sparkfun/SuperHeadphones/docs/assets/board_files/Super_Headphones_Dimensions.png

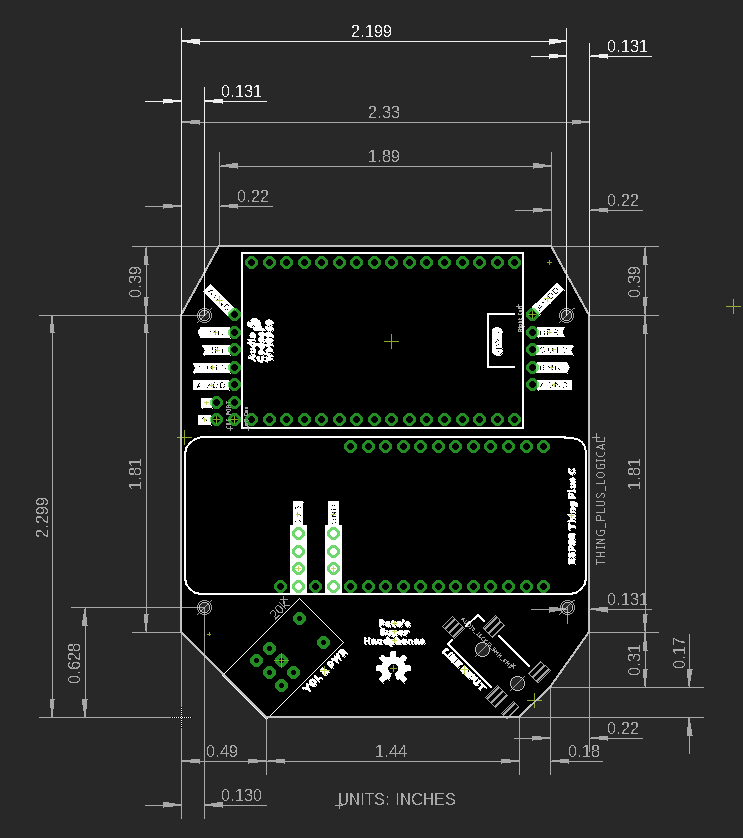
docs/assets/board_files/Super_Headphones_Dimensions.png
