sparkfun/SuperHeadphones/docs/assets/img/cell_bt_connect.jpg

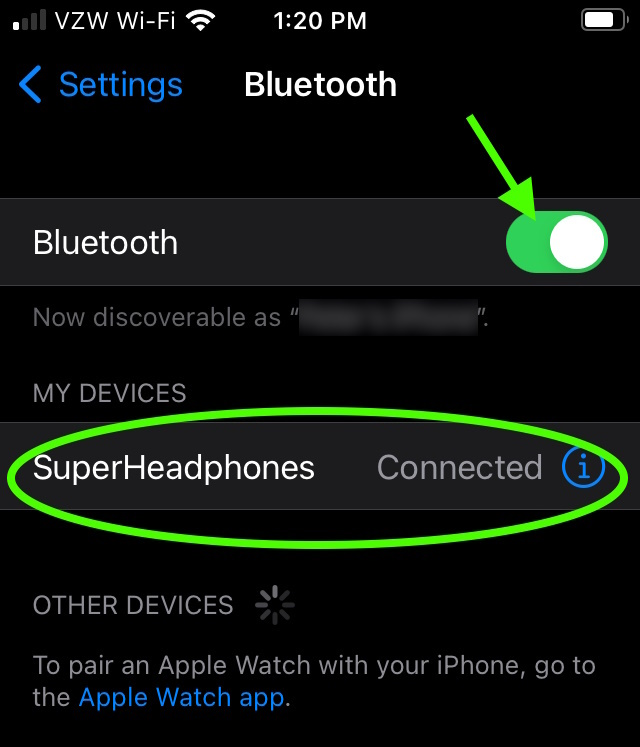
docs/assets/img/cell_bt_connect.jpg
