sparkfun/SuperHeadphones/docs/assets/img/hps_315wide.jpg

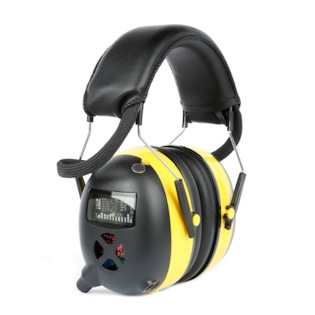
docs/assets/img/hps_315wide.jpg
