sparkfun/SuperHeadphones/docs/assets/img/pc_bt_connect.png

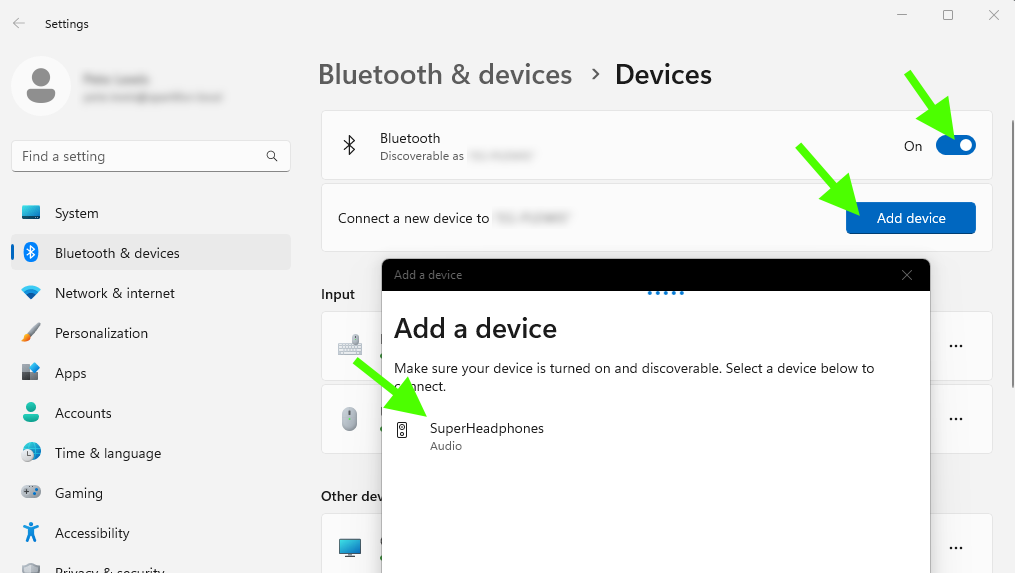
docs/assets/img/pc_bt_connect.png
