sparkfun/SuperHeadphones/docs/assets/img/pete_rotate.gif

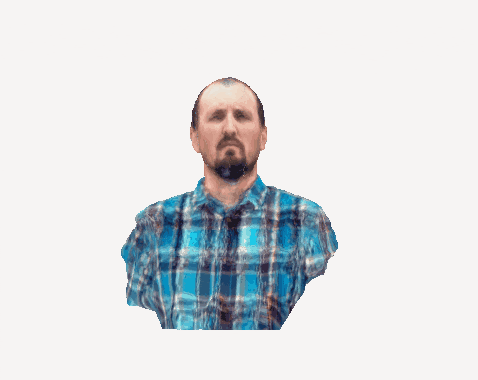
docs/assets/img/pete_rotate.gif
