sparkfun/SuperHeadphones/docs/assets/img/Super_Headphones_Block_Diagram_v01.jpg

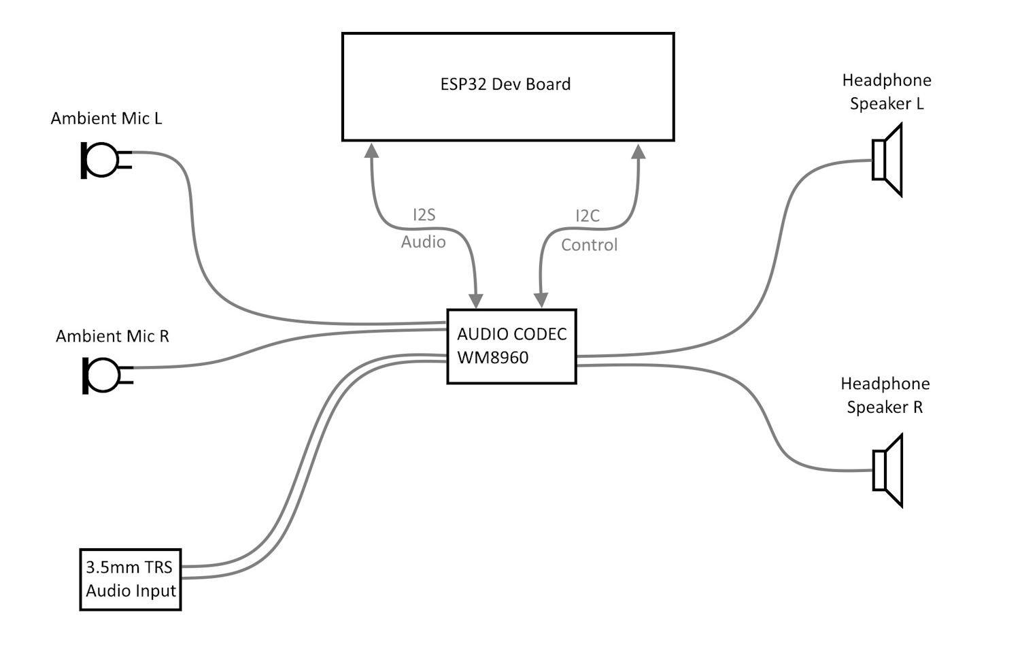
docs/assets/img/Super_Headphones_Block_Diagram_v01.jpg
