sparkfun/SuperHeadphones/docs/assets/img/thumbnail.jpg

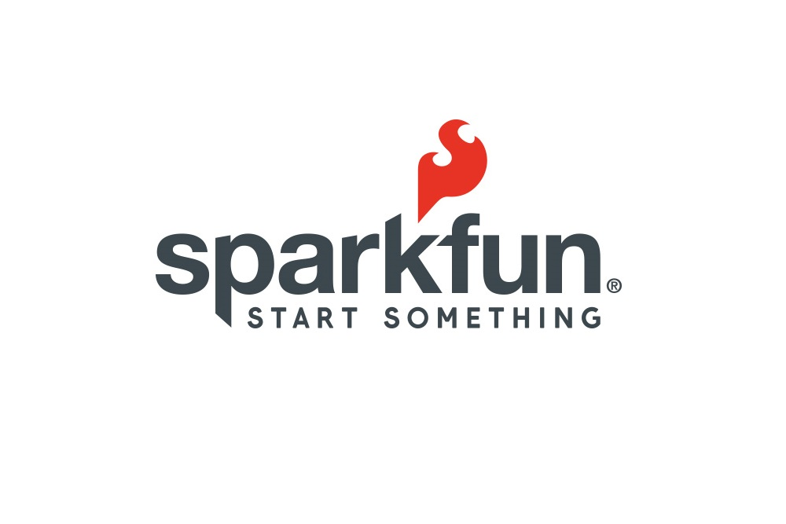
docs/assets/img/thumbnail.jpg
